psytraxx/gravity-cube-rs/desktop/src/camera.rs

use glam::camera::rh::proj::directx::perspective;
use glam::camera::rh::view::look_at_mat4;
use glam::{Mat4, Vec3};

pub struct Camera {
    pub position: Vec3,
    pub target: Vec3,
    pub up: Vec3,
    pub fov: f32,
    pub aspect: f32,
    pub near: f32,
    pub far: f32,
}

impl Camera {
    pub fn new(aspect: f32) -> Self {
        Self {
            position: Vec3::new(0.0, 0.0, 35.0),
            target: Vec3::new(3.5, 3.5, 3.5), // Center of 8x8x8 cube
            up: Vec3::Y,
            fov: 45.0_f32.to_radians(),
            aspect,
            near: 0.1,
            far: 100.0,
        }
    }

    pub fn update_aspect(&mut self, aspect: f32) {
        self.aspect = aspect;
    }

    pub fn view_matrix(&self) -> Mat4 {
        look_at_mat4(self.position, self.target, self.up)
    }

    pub fn projection_matrix(&self) -> Mat4 {
        // directx: clip-space depth range 0..1, matching wgpu's convention.
        perspective(self.fov, self.aspect, self.near, self.far)
    }

    pub fn view_projection_matrix(&self) -> Mat4 {
        self.projection_matrix() * self.view_matrix()
    }
}
